frescolabs/FrescoM/hardware/print/manifold_extrusion_holder.stl

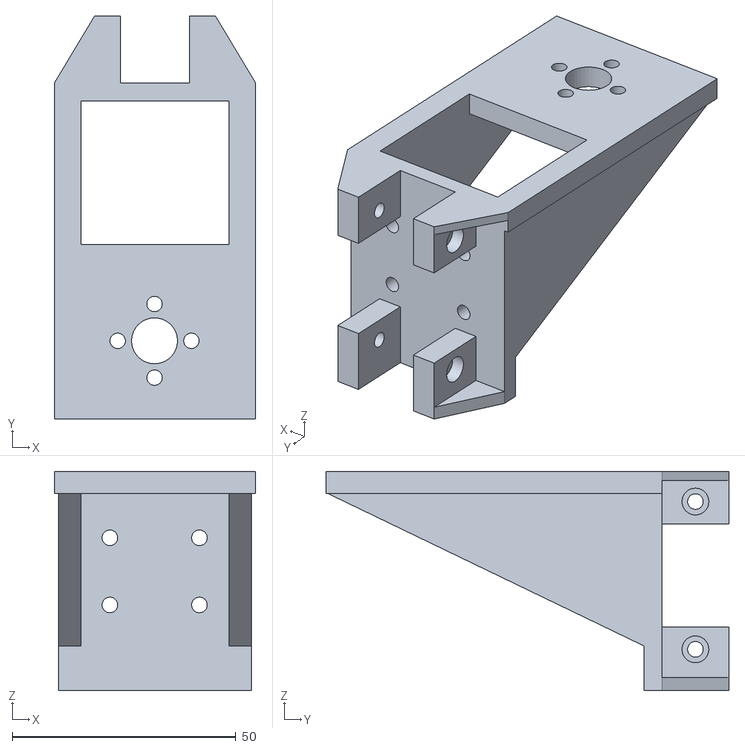
[picture p29: CAD file, 2021-02-09]
hardware/print/manifold_extrusion_holder.stl
45.0 x 90.0 x 49.0
