frescolabs/FrescoM/hardware/print/y_plate_holder.stl

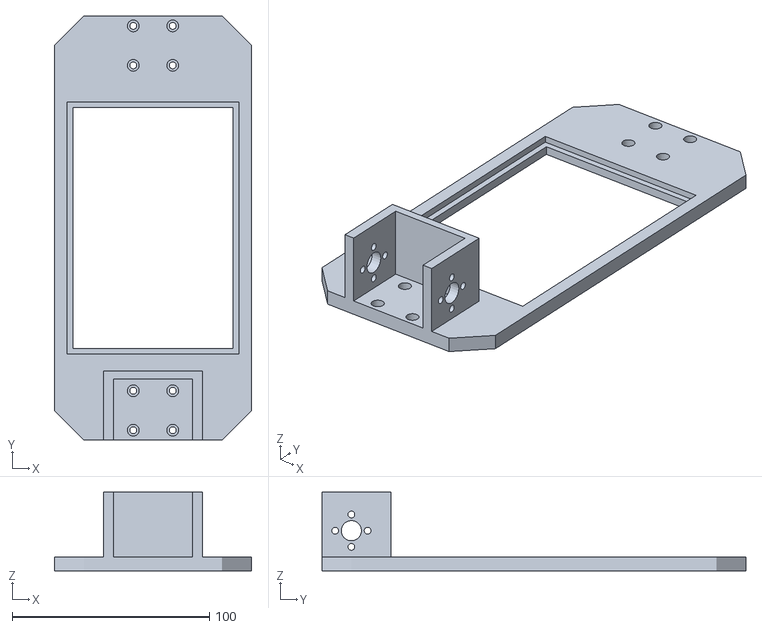
[picture p30: CAD file, 2021-02-09]
hardware/print/y_plate_holder.stl
100.0 x 215.0 x 40.0
