frescolabs/FrescoM/hardware/print/manifold_nema_cap.stl

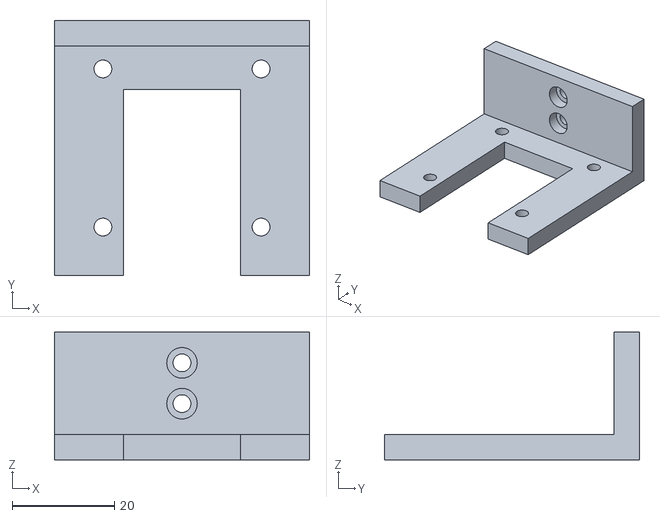
[picture p31: CAD file, 2021-02-09]
hardware/print/manifold_nema_cap.stl
50.0 x 50.0 x 25.0
