frescolabs/FrescoM/hardware/print/x_stopper_holder.stl

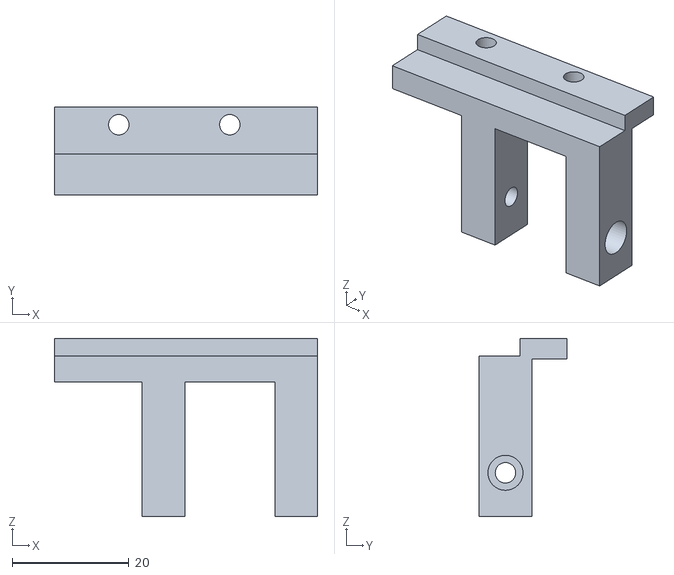
[picture p32: CAD file, 2021-02-09]
hardware/print/x_stopper_holder.stl
45.0 x 15.0 x 30.5
