frescolabs/FrescoM/firmware/FrescoMFirmware/FrescoXYZ.h

#ifndef FrescoXYZ_h
#define FrescoXYZ_h

#include "MotorController.h"
#include "Command.h"
#include "Point.h"
#include "Manifold.h"
#include "MOSFETLED.h"
#include "DriverLED.h"
#include "Responder.h"

// Contains all motor controllers
class FrescoXYZ {

  private:
  
    MotorController* xMotorController;
    MotorController* yMotorController;
    MotorController* zMotorController;
    Manifold* manifold;
    MOSFETLED* whiteLed;
    DriverLED* blueLed;
    Responder *responder;
    
    long xLeftPostition;
    long xRightPosition;
    long yTopPosition;
    long yBottomPosition;
    long xLength;
    long yLength;

  void saveBottomRightPosition();
  void saveTopLeftPosition();
  Point restoreBottomRightPosition();
  Point restoreTopLeftPosition();
  
  public:
  
  FrescoXYZ(MotorController* xMotorController, 
            MotorController* yMotorController, 
            MotorController* zMotorController,
            Manifold* manifold,
            MOSFETLED* whiteLed,
            DriverLED* blueLed);

  void setPosition(long x, 
                   long y, 
                   long z);
  
  void moveDelta(long x, 
                 long y, 
                 long z);

  void goToZero();
  long getXLength();
  long getYLength();
  Point getBottomRight();
  Point getTopLeft();
  long EEPROMReadlong(long address);
  void EEPROMWritelong(int address, long value);
  
  void perform(Command command);
  
};

#endif
