frescolabs/FrescoM/firmware/FrescoMFirmware/Pins.h

#ifndef Pins_h
#define Pins_h

#define EN 13
#define NUM_MOTORS 12

// Leds
#define LEDW 48
#define LEDB 46

// CNC1 
#define XS1 5
#define YS1 6
#define ZS1 7
#define XD1 8
#define YD1 9
#define ZD1 10
#define AS1 11
#define AD1 12

// CNC2  
#define XS2 27
#define YS2 29
#define ZS2 31
#define AS2 23
#define XD2 33
#define YD2 35
#define ZD2 37 
#define AD2 25

// CNC3
#define XS3 43
#define YS3 45
#define ZS3 47
#define AS3 37
#define XD3 49
#define YD3 51
#define ZD3 53
#define AD3 41

// End stops
#define ES1 22
#define ES2 24
#define ES3 26
#define ES4 28
#define ES5 30
#define ES6 32
#define ES7 34
#define ES8 36
#define ES9 38
#define ES10 40
#define ES11 42
#define ES12 44

#endif
